djtersteegc/fujinet-adam-hardware/docs/devkit-mini-cased.jpg

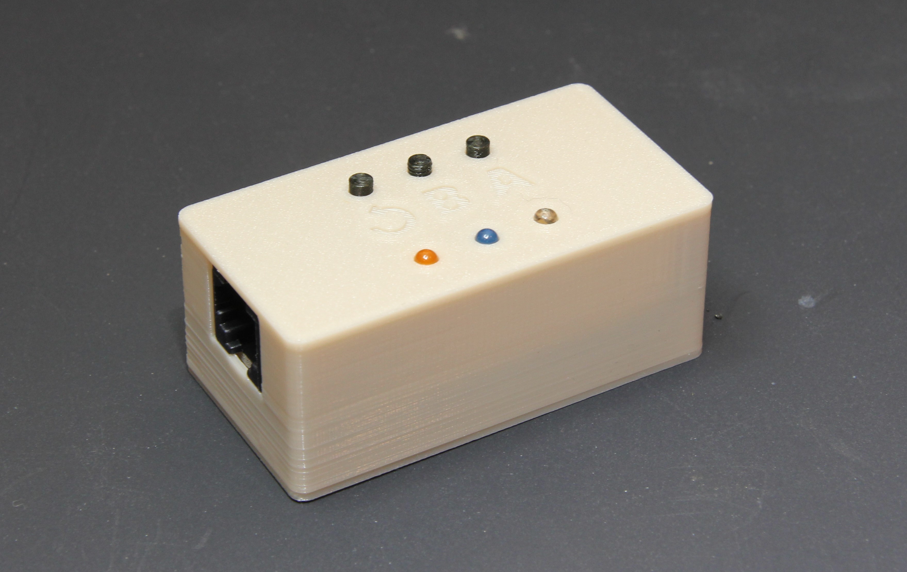
docs/devkit-mini-cased.jpg
